gabrielhipolito-dev/rc_controller/rc_controller/img/arduino_transparent.png

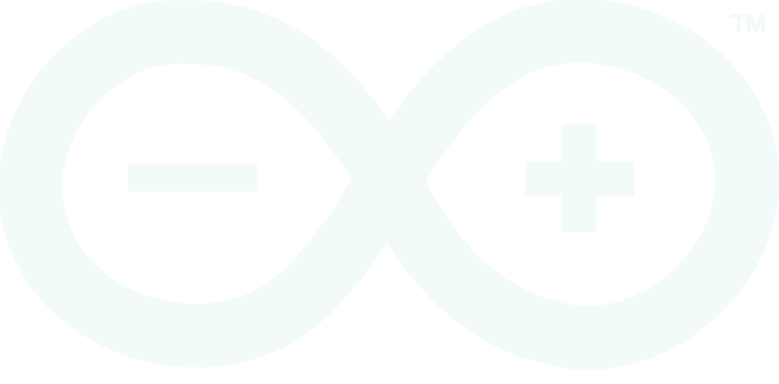
rc_controller/img/arduino_transparent.png
