gabrielhipolito-dev/rc_controller/rc_controller/img/arm-back.png

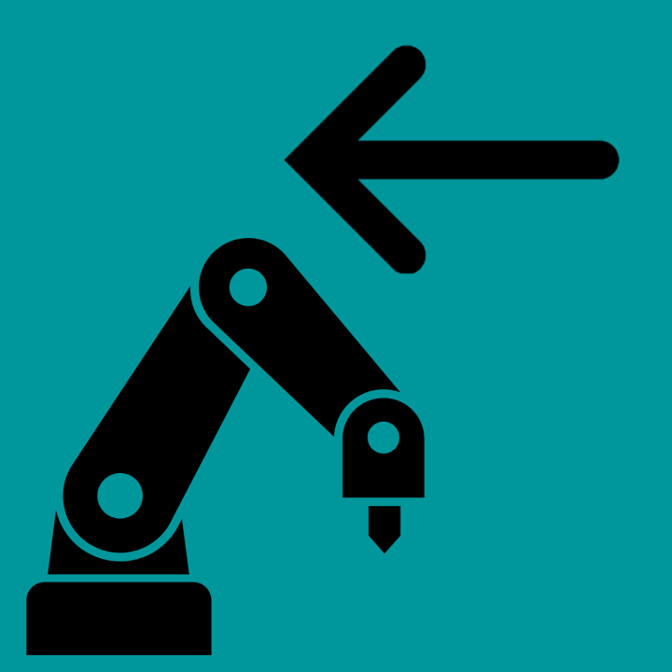
rc_controller/img/arm-back.png
