gabrielhipolito-dev/rc_controller/rc_controller/img/arm-down.png

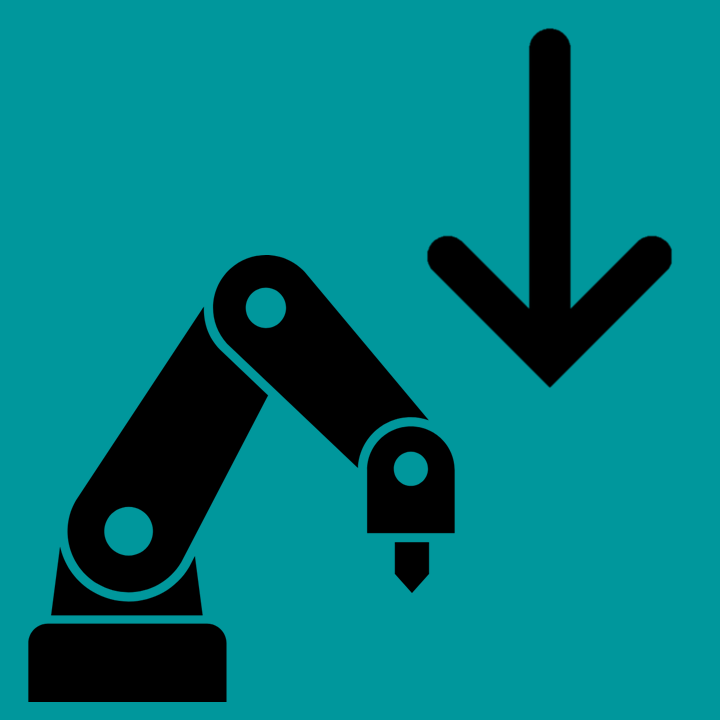
rc_controller/img/arm-down.png
