gabrielhipolito-dev/rc_controller/rc_controller/img/arrow-down.png

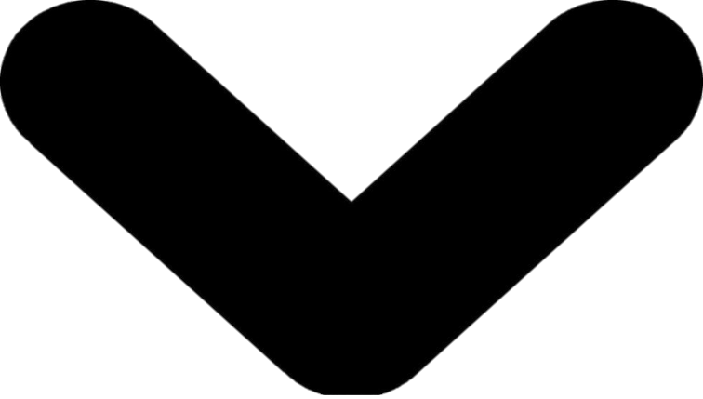
rc_controller/img/arrow-down.png
