gabrielhipolito-dev/rc_controller/rc_controller/img/arrow-left.png

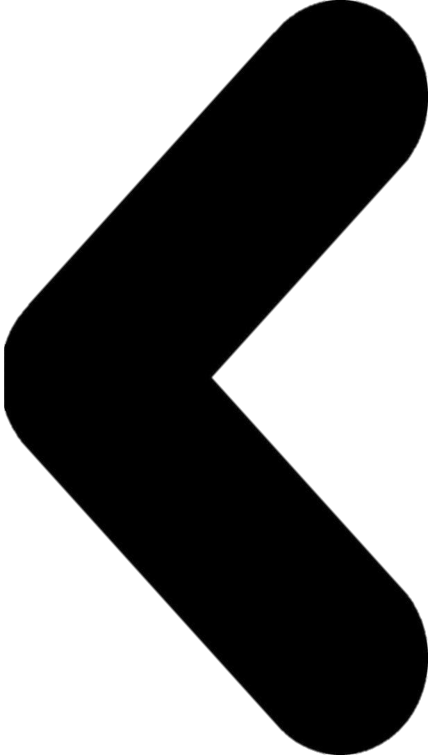
rc_controller/img/arrow-left.png
