gabrielhipolito-dev/rc_controller/rc_controller/img/arrow-up.png

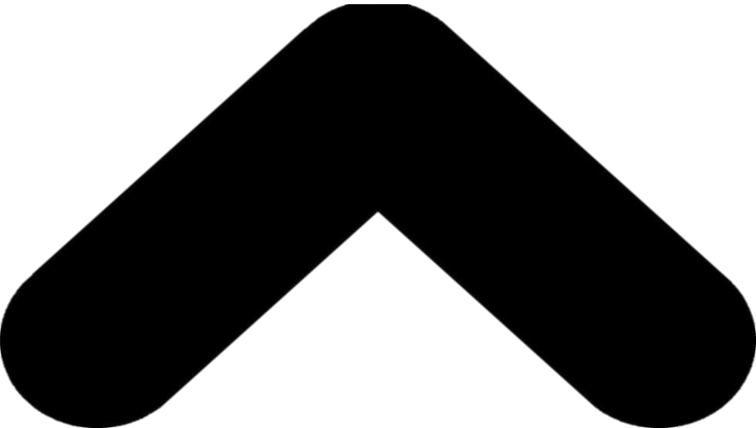
rc_controller/img/arrow-up.png
