gabrielhipolito-dev/rc_controller/rc_controller/img/motor-down.png

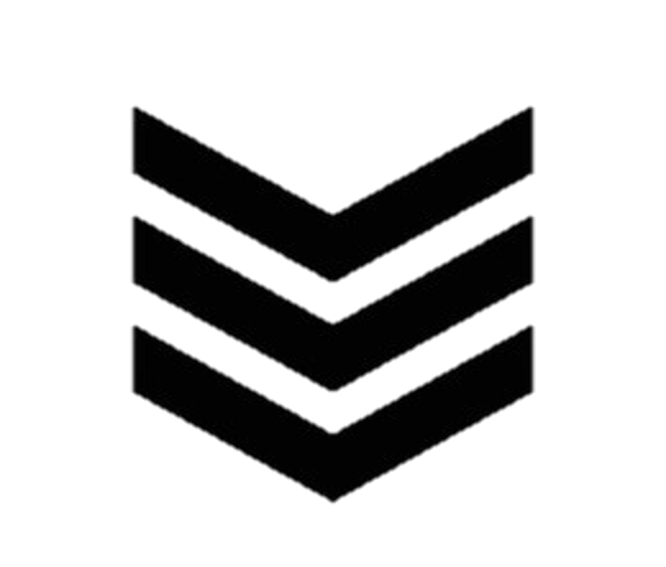
rc_controller/img/motor-down.png
