gabrielhipolito-dev/rc_controller/rc_controller/img/motor-up.png

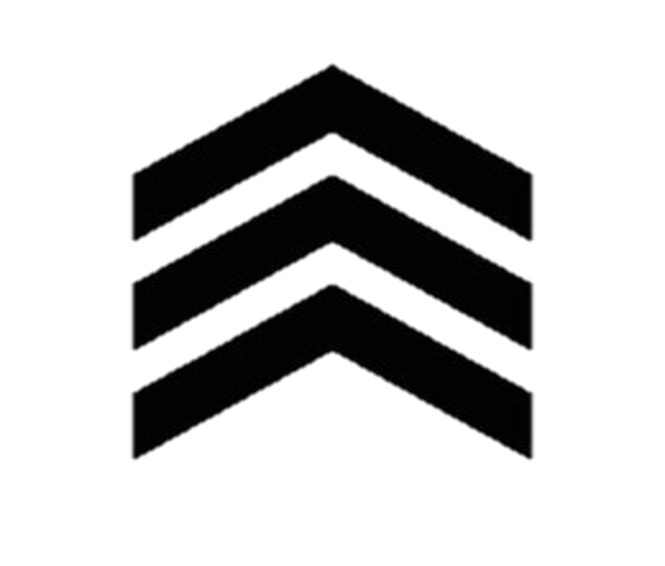
rc_controller/img/motor-up.png
