gabrielhipolito-dev/rc_controller/rc_controller/img/plus.png

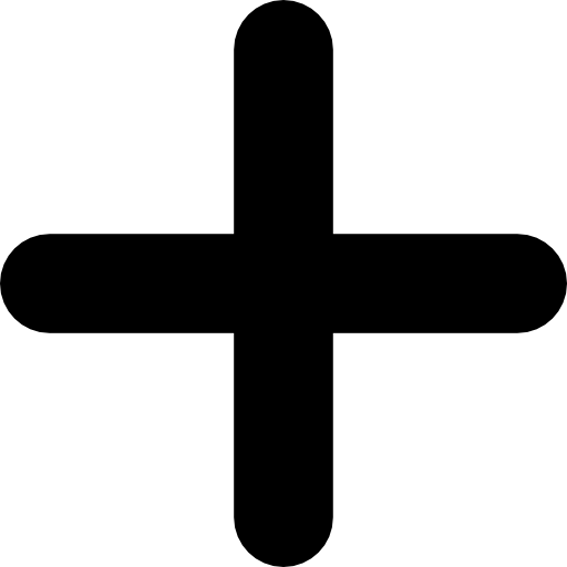
rc_controller/img/plus.png
