gabrielhipolito-dev/rc_controller/rc_controller/3D parts/ara-another-robot-arm-model_files/Arms & Base/Arm_C2 Triangle.stl

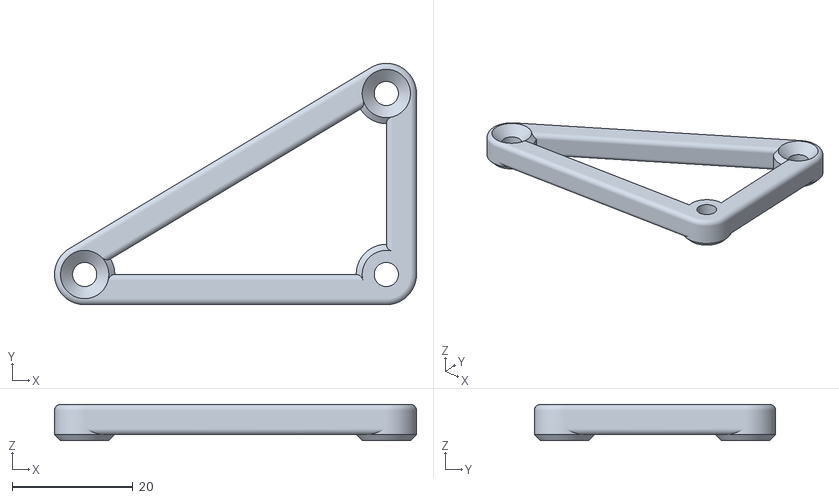
[picture p34: CAD file, 2025-11-04, last stored version]
rc_controller/3D parts/ara-another-robot-arm-model_files/Arms & Base/Arm_C2 Triangle.stl
60.0 x 40.0 x 6.00
