gabrielhipolito-dev/rc_controller/rc_controller/3D parts/ara-another-robot-arm-model_files/End Effector/Gripper_ServoArm - Part 1.stl

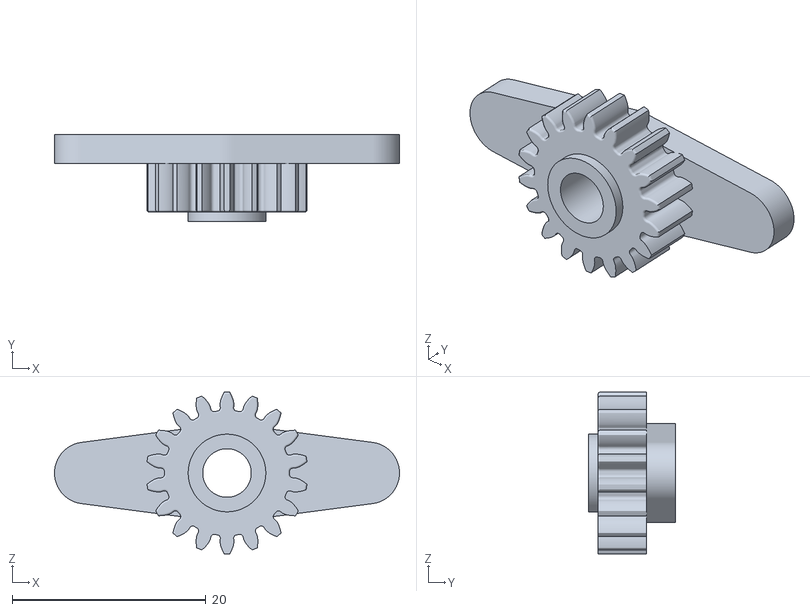
[picture p35: CAD file, 2025-11-04, last stored version]
rc_controller/3D parts/ara-another-robot-arm-model_files/End Effector/Gripper_ServoArm - Part 1.stl
35.6 x 9.00 x 16.7
