gabrielhipolito-dev/rc_controller/rc_controller/3D parts/ara-another-robot-arm-model_files/Arms & Base/MountPlate - BasePlate.stl

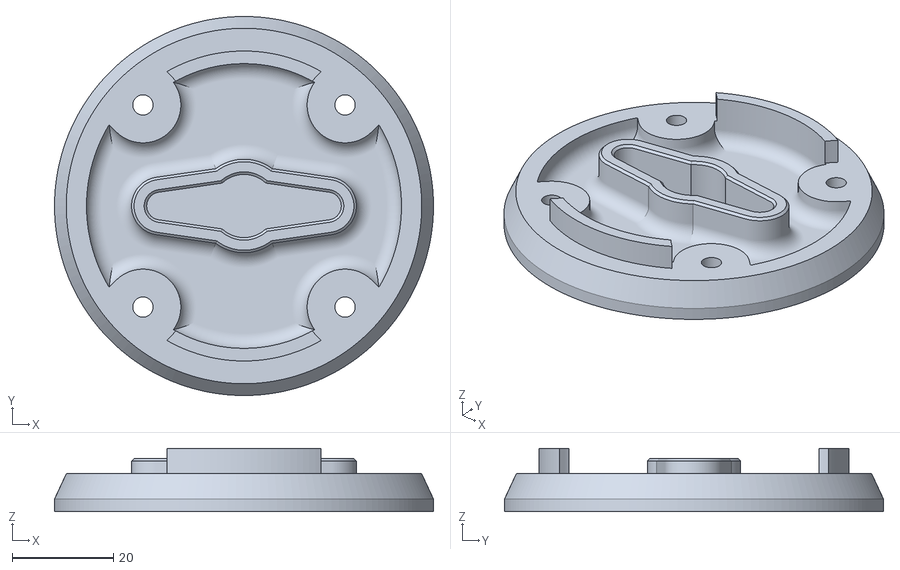
[picture p36: CAD file, 2025-11-04, last stored version]
rc_controller/3D parts/ara-another-robot-arm-model_files/Arms & Base/MountPlate - BasePlate.stl
75.0 x 75.0 x 12.5
