gabrielhipolito-dev/rc_controller/rc_controller/3D parts/ara-another-robot-arm-model_files/End Effector/Grip_base - Part 1.stl

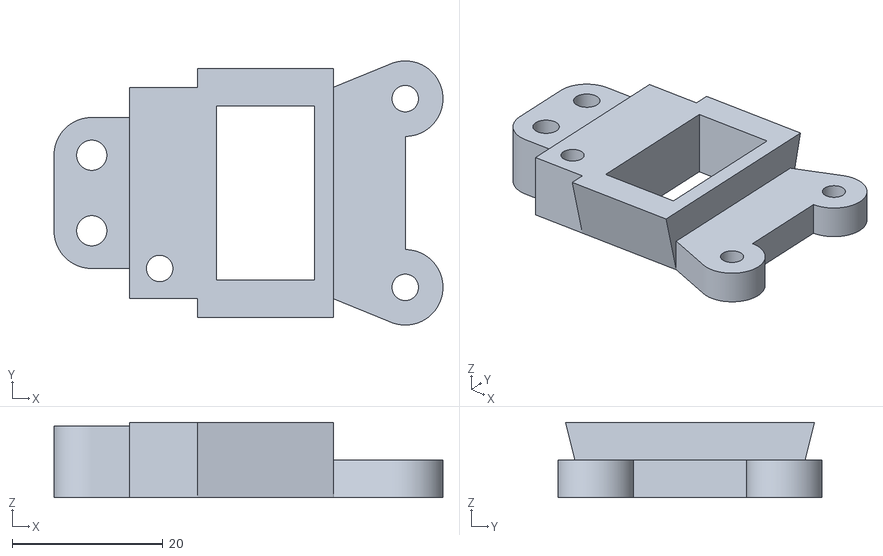
[picture p37: CAD file, 2025-11-04, last stored version]
rc_controller/3D parts/ara-another-robot-arm-model_files/End Effector/Grip_base - Part 1.stl
51.5 x 35.0 x 10.0
