gabrielhipolito-dev/rc_controller/rc_controller/3D parts/ara-another-robot-arm-model_files/Arms & Base/Arm_C3.stl

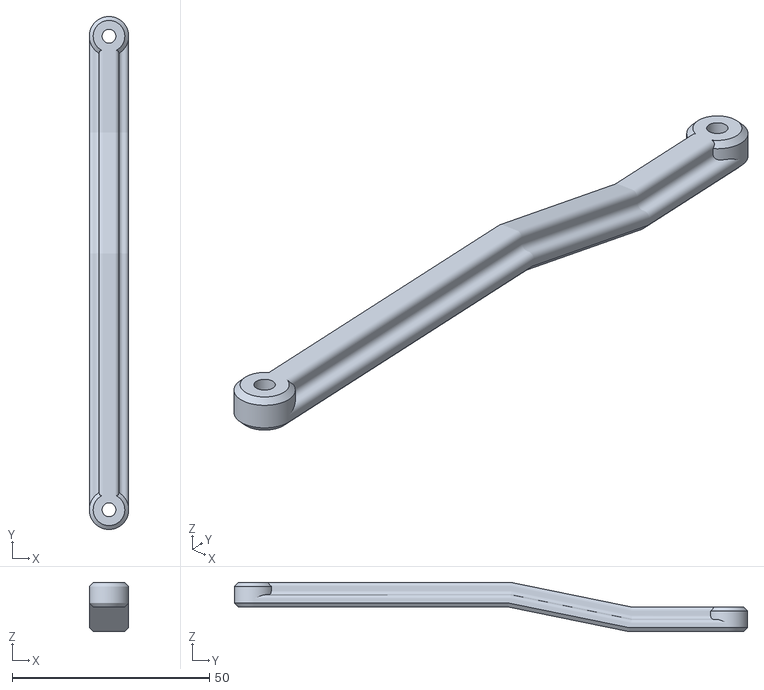
[picture p38: CAD file, 2025-11-04, last stored version]
rc_controller/3D parts/ara-another-robot-arm-model_files/Arms & Base/Arm_C3.stl
10.0 x 130.0 x 12.5
