gabrielhipolito-dev/rc_controller/rc_controller/3D parts/ara-another-robot-arm-model_files/Arms & Base/Base.stl

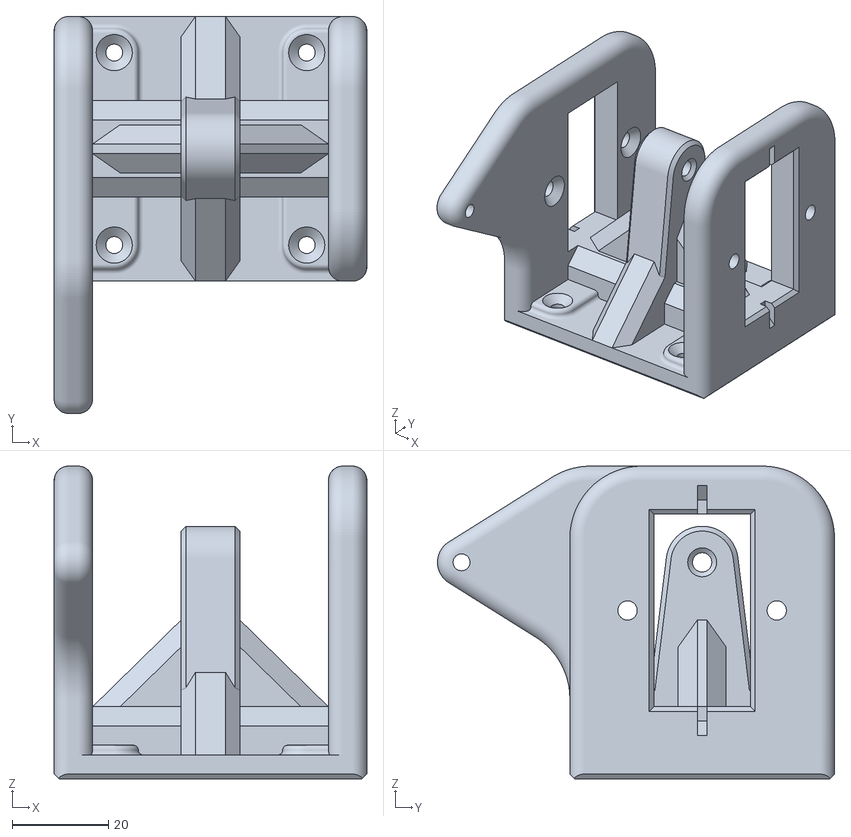
[picture p39: CAD file, 2025-11-04, last stored version]
rc_controller/3D parts/ara-another-robot-arm-model_files/Arms & Base/Base.stl
65.0 x 82.5 x 65.0
